labsir-un/3DModels_KIT_Phantom_Pincher_X100/Documentacion/MONOGRAFIA_KIT/Trabajo_de_grado/01preambulo/presentacion.tex

%Páginas de Presentación del documento - No modificar esto se hace automáticamente
{\newpage
\thispagestyle{empty}
\begin{center}
    \begin{figure}
        \centering
        \epsfig{file=00Figuras/00f00EscudoUN2016,scale=1}%
        \end{figure}
    \vspace{2.5cm}
    \textbf{\Huge \thesisname} \\ 
    \vspace{2.5cm}
    \textbf{\Large \studentname} \\
    \vspace{5.0cm}
    \faculty \\ \department \\
    \sede, Colombia Bogotá\\
    \issuedate
    \newpage 
    \thispagestyle{empty}
    \vspace{2.0cm}
    %\small Nota: No utilizar el tipo de letra Ancizar en el documento puesto que este tipo de fuente restringe la copia de los archivos en el Repositorio Institucional. [Recuerde borrar esta nota]\\
    \textbf{\Huge \thesisname} \\
    \vspace{3.0cm}
    \textbf{\Large \studentname} \\
    \vspace{3.0cm}
    \small Trabajo de grado presentado como requisito parcial para optar por el título de: \\
    {\bfseries \academictitle}\\
    \vspace{3.0cm}
    \textbf{Director:} \\
    \director \\
    \directortitle \; - \department \\
    \faculty \\
    \university \\ 
    \vspace{5cm}
    %\textbf{Codirector(a):} \\
    %\codirector \\
    %\codirectortitle \; - \department \\
    %\faculty \\
    %\university 
    %\vspace{1.5cm} \\
    %\textbf{Línea de investigación:} \\ 
    %\researchtopic\\
    %\textbf{Grupo de investigación:} \\
    %\resgroupone \\
    %\resgrouptwo \\
    %\vspace{1.5cm}
    \university \\
    \faculty \\
    \department \\
    \issuedate
\end{center}

% Dedicatorias
\newpage
\thispagestyle{empty}
\begin{flushright}
    \begin{minipage}{12.5cm}
        \noindent
        \\[10em]
        %Modificar la cita que se quiere agregar
        {\Large Cita 01.}
        \\[3em]
         DEMING, W. Edward.
        \\ \textit{Out of the crisis. Cambridge: MIT Press, 1986.}
        \\[10em]
        %Para anular la adición de una segunda cita anule las siguientes lineas desde acá mediante comentario (%)
        {\Large \textit{It is not enough to do your best; you must first know what to do, and then do your best.} - No basta con hacer lo mejor que podemos; primero debemos saber qué hacer, y luego hacer lo mejor que podamos.}
        \\[3em]
        DEMING, W. Edward.
        %Hasta acá!
    \end{minipage}
\end{flushright} 

% Declaracíon de originalidad del texto y del contenido
% No modificar, se hace automáticamente con los comandos ya definidos
\newpage
\chapter*{\sffamily Declaración}
\par Me permito afirmar que he realizado este trabajo de grado de manera autónoma y con la única ayuda de los medios permitidos y no diferentes a los mencionados el presente texto. Todos los pasajes que se han tomado de manera textual o figurativa de textos publicados y no publicados, los he reconocido en el presente trabajo. Ninguna parte del presente trabajo se ha empleado en ningún otro tipo de trabajo de grado. 
\\[1em]
\sede., \submissiondate
\\[6em]
\rule{6cm}{0.5pt}\\
\studentname
}
