labsir-un/3DModels_KIT_Phantom_Pincher_X100/Documentacion/MONOGRAFIA_KIT/Trabajo_de_grado/01preambulo/tablasContenido.tex

% Dejar esta parte así para que genere correctamente la página de la tabla de contenido
\addcontentsline{toc}{chapter}{Lista de figuras}
\listoffigures
\clearpage
\addcontentsline{toc}{chapter}{Lista de tablas}
\listoftables
\clearpage
\addcontentsline{toc}{chapter}{Contenido}
\tableofcontents
\clearpage
