labsir-un/3DModels_KIT_Phantom_Pincher_X100/Documentacion/MONOGRAFIA_KIT/Trabajo_de_grado/02intro/Objetivos.tex

\section{Objetivo General}

Diseñar un kit educativo para la clasificación de objetos mediante visión por computador, empleando el robot PhantomX Pincher, la plataforma Raspberry Pi 5 y el sistema operativo robótico ROS2, con base en referentes comerciales y criterios académicos de aplicabilidad y funcionalidad.

\section{Objetivos Específicos}

\begin{enumerate}
    \item Identificar los requerimientos de hardware y software necesarios para un sistema de clasificación de objetos basado en visión artificial con ROS2 y Raspberry Pi 5.
    
    \item Diseñar conceptualmente la estructura física del kit, incluyendo el montaje de cámara, elementos de sujeción, gripper o ventosa, y disposición de componentes electrónicos.
    
    \item Proponer una arquitectura de software basada en ROS2 que contemple nodos para captura de imagen, procesamiento visual, clasificación de objetos y control del manipulador.
    
    \item Desarrollar simulaciones en entornos compatibles con ROS2 para observar el comportamiento esperado del sistema y el flujo de operación.
    
    \item Establecer lineamientos para una futura implementación del kit en entornos educativos, considerando aspectos de escalabilidad, modularidad y documentación pedagógica.
    
    \item Construir un prototipo físico básico del kit de clasificación de objetos, utilizando componentes disponibles, con el fin de ilustrar de manera práctica el diseño propuesto.
\end{enumerate}
