labsir-un/3DModels_KIT_Phantom_Pincher_X100/Documentacion/MONOGRAFIA_KIT/Trabajo_de_grado/05requerimientos/reque.tex

\section{Síntesis de Requerimientos Definidos}

A partir de las respuestas proporcionadas, se establecen los siguientes requerimientos principales para el proyecto:

\subsection{Requerimientos Cuantitativos}
\begin{itemize}
    \item Número de kits a desarrollar: 7 unidades
    \item Presupuesto máximo por kit: \$600,000 COP (sin incluir electrónica)
    \item Plazo de entrega: Semana 8 del semestre 2025-2
    \item Cursos de aplicación: Robótica (exclusivamente)
\end{itemize}

\subsection{Requerimientos de Hardware}
\begin{itemize}
    \item Sistema de visión: Cámara integrada
    \item Sistema de sujeción: Copa de succión (como sistema principal)
    \item Sistema de sujeción alternativo: Conservar pinza original
    \item Modificaciones permitidas: Base del robot
    \item Componentes a mantener: Eslabones 1, 2 y 3 originales
    \item Electrónica: Posibilidad de reemplazo y reubicación
    \item Componentes excluidos: Pantalla LCD
\end{itemize}

\subsection{Requerimientos de Software}
\begin{itemize}
    \item Framework principal: ROS2
    \item Biblioteca de visión: OpenCV
    \item Lenguaje de programación: Python
    \item Funcionalidad principal: Reconocimiento de imágenes y visión de máquina
\end{itemize}

\subsection{Requerimientos de Documentación}
\begin{itemize}
    \item Repositorio principal: Organización LabSIR en GitHub
    \item Contenido del repositorio:
    \begin{itemize}
        \item Guías de usuario
        \item Diseño mecánico del kit
        \item Modelos 3D
        \item Respaldo del sistema operativo de los controladores
    \end{itemize}
    \item Material complementario: Videos e imágenes
    \item Plataforma de videos: Canal de LabSIR en YouTube
    \item Referencia: Guías anteriores del curso de Robótica
\end{itemize}

\subsection{Requerimientos Logísticos}
\begin{itemize}
    \item Espacios de trabajo: SalaCAM o Laboratorio de Automatización
    \item Horarios: Flexibles, a definir según disponibilidad
    \item Acceso a material previo: Guías y desarrollos anteriores de ROS disponibles para consulta
\end{itemize}
