labsir-un/3DModels_KIT_Phantom_Pincher_X100/Documentacion/MONOGRAFIA_KIT/Trabajo_de_grado/apendices/apendice_cuestionario.tex

\chapter{Apendice: Cuestionario de Preguntas sobre el Proyecto}

Este apéndice contiene el cuestionario elaborado para el director del proyecto, con el fin de clarificar aspectos técnicos, presupuestales, estructurales y metodológicos relacionados con el desarrollo del kit de clasificación de objetos para el robot PhantomX Pincher.

\section{Requerimientos Generales del Proyecto}

\begin{enumerate}
    \item \textbf{¿La fecha aproximada para la terminación del proyecto es para la semana 8 del semestre 2025-1 o para la semana 8 del semestre 2025-2?}
    
    \item \textbf{¿Cuántos Robot PhantomX Pincher hay en el laboratorio?}
    
    \item \textbf{¿Para cuántos de estos Robots se debe construir el kit?}
    
    \item \textbf{¿Existe un presupuesto para la construcción de cada kit? De ser así, ¿cuál es el presupuesto? (IMPORTANTE)}
\end{enumerate}

\section{Cambios Estructurales y Estética del Robot}

\begin{enumerate}[resume]
    \item \textbf{¿Qué partes actuales del robot se deben o pueden modificar?}
    
    \begin{figure}[H]
    \centering
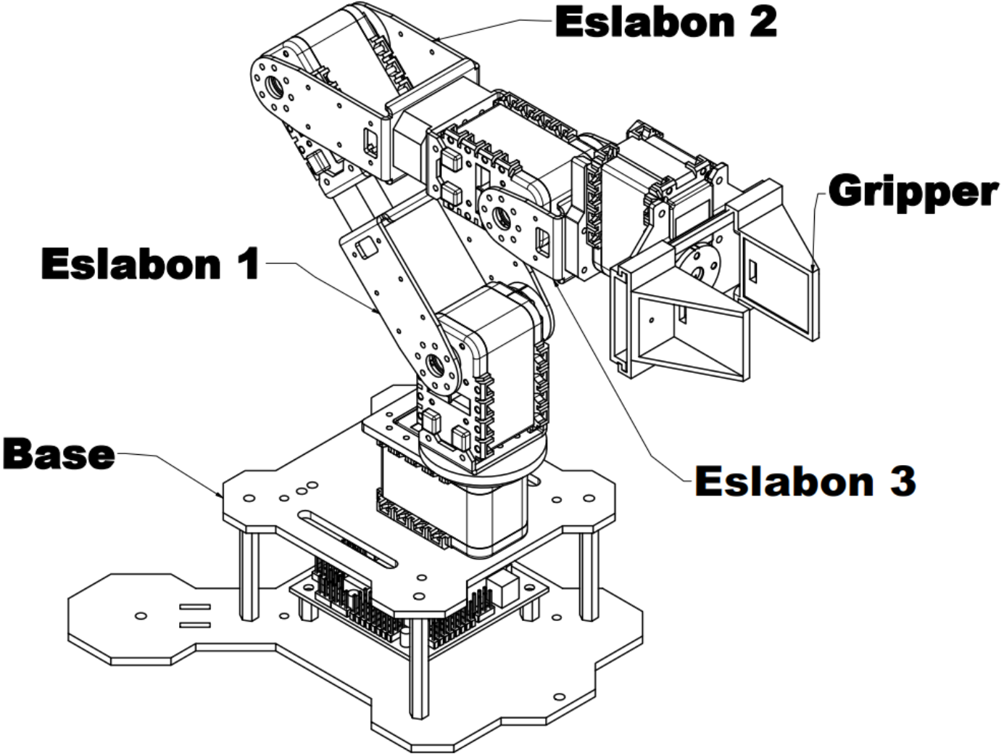
[picture p79: Documentacion/MONOGRAFIA_KIT/Trabajo_de_grado/apendices/img/phantomx_pincher_diagram.png]
    
    \caption{Diagrama del Robot PhantomX Pincher mostrando sus principales componentes: Base, Eslabón 1, Eslabón 2, Eslabón 3, y Gripper}
    \label{fig:phantomx_diagram}
    \end{figure}
    
    \item \textbf{¿Se desea reemplazar el eslabón 1?}
    
    \textit{Razón de la pregunta: es para saber si se quiere que la estética general del robot se parezca a la del kit de Elephant Robotics}
    
    \item \textbf{¿Se desea reemplazar el eslabón 2?}
    
    \textit{Razón de la pregunta: es para saber si se quiere que la estética general del robot se parezca a la del kit de Elephant Robotics}
    
    \item \textbf{¿Se desea reemplazar el eslabón 3?}
    
    \textit{Razón de la pregunta: es para saber si se quiere que la estética general del robot se parezca a la del kit de Elephant Robotics}
    
    \item \textbf{¿Se puede reemplazar la base del robot?}
    
    \item \textbf{¿Se puede desplazar la electrónica de la base a otra área?}
    
    \item \textbf{¿Se desea tener una copa de succión como en el kit de Elephant Robotics o se puede seguir usando el gripper del Pincher?}
\end{enumerate}

\section{Kit para PhantomX Pincher en Relación con myCobot AI Kit}

\subsection{Estructura de Composición del Sistema en Hardware}

\begin{enumerate}[start=12]
    \item \textbf{Referente a la estructura de composición del sistema del kit en hardware, ¿qué se desea tener de la siguiente lista?}
    
    \begin{itemize}
        \item Brazo mecánico
        \item Base fija
        \item Bomba de succión
        \item Cámara
        \item Módulo identificable
    \end{itemize}
\end{enumerate}

\subsection{Estructura de Composición del Sistema en Software}

\begin{enumerate}[start=13]
    \item \textbf{Referente a la estructura de composición del sistema del kit en software, ¿qué se desea tener de la siguiente lista?}
    
    \begin{itemize}
        \item Módulo de agarre
        \item Módulo de reconocimiento de imágenes
    \end{itemize}
\end{enumerate}

\subsection{Componentes del Kit myCobot AI Kit}
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
