labsir-un/3DModels_KIT_Phantom_Pincher_X100/Documentacion/MONOGRAFIA_KIT/Trabajo_de_grado/conclusiones/conlusiones.tex

Este trabajo cumplió con el objetivo general de diseñar un kit educativo para la clasificación de objetos mediante visión por computador empleando el robot PhantomX Pincher, la plataforma Raspberry Pi 5 y el sistema operativo robótico ROS2. Los objetivos específicos se alcanzaron completamente.
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
