labsir-un/3DModels_KIT_Phantom_Pincher_X100/Documentacion/MONOGRAFIA_KIT/Trabajo_de_grado/apendices/img/mycobot_components.webp

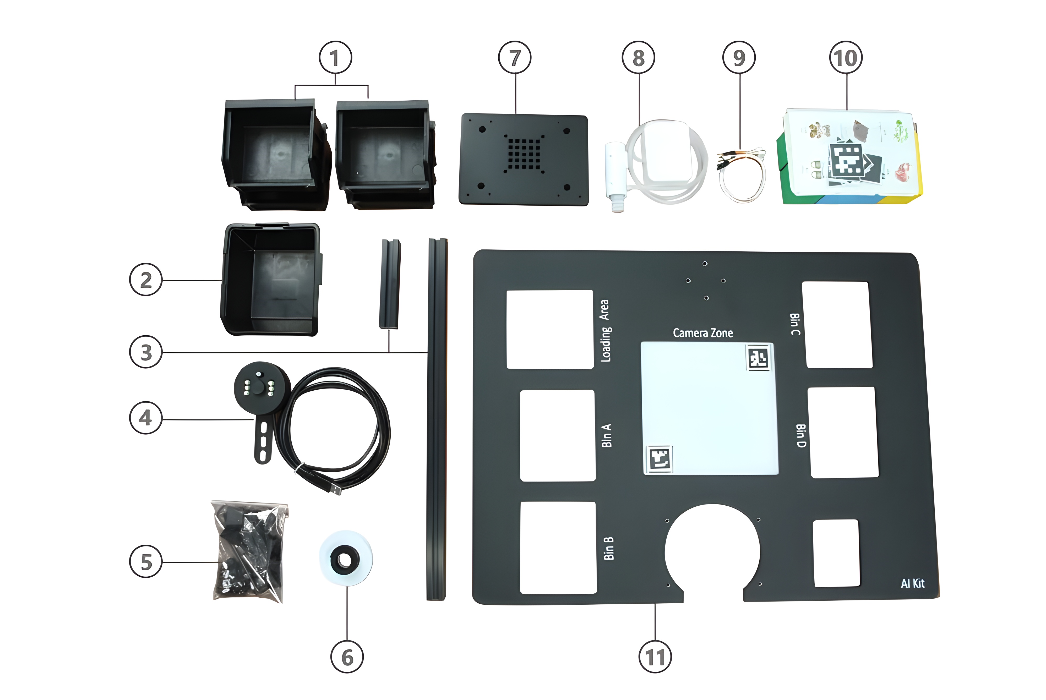
Documentacion/MONOGRAFIA_KIT/Trabajo_de_grado/apendices/img/mycobot_components.webp
